dlandry97/Shear_Haptics/Unity_Project/The Haptic Dojo/Assets/SteamVR/Models/Materials/vr_glove_normal.png

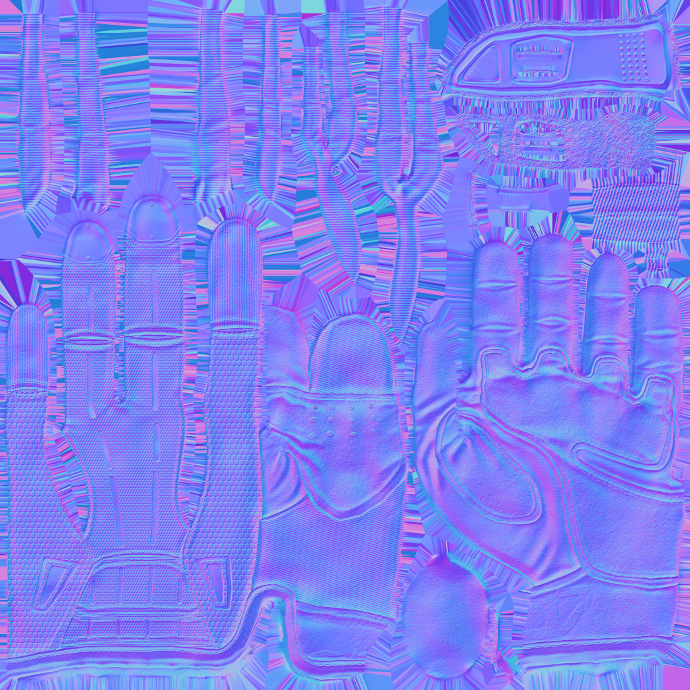
Unity_Project/The Haptic Dojo/Assets/SteamVR/Models/Materials/vr_glove_normal.png
