dlandry97/Shear_Haptics/Unity_Project/The Haptic Dojo/Assets/Katana/Texture/PNG/Katana_AO.png

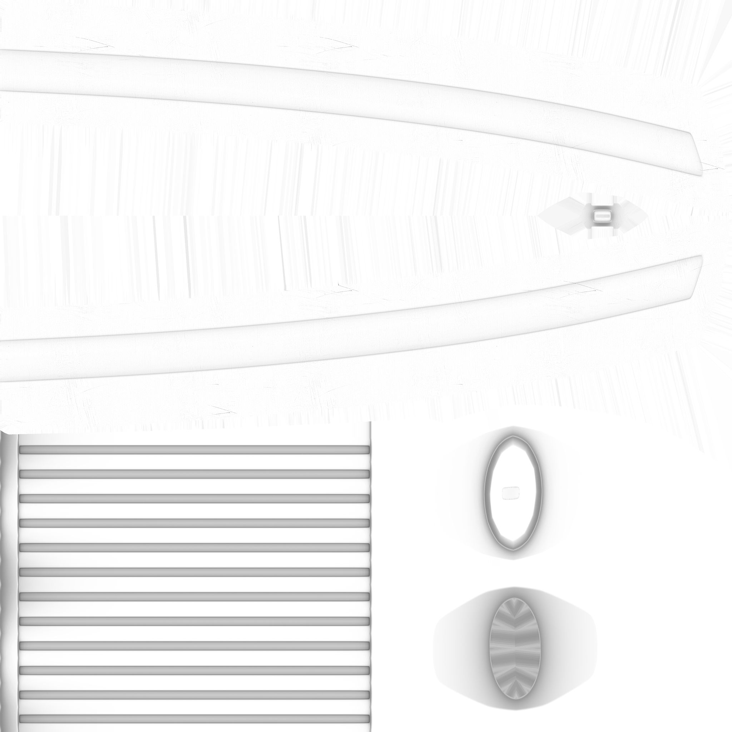
Unity_Project/The Haptic Dojo/Assets/Katana/Texture/PNG/Katana_AO.png
