dlandry97/Shear_Haptics/Unity_Project/The Haptic Dojo/Assets/Katana/Texture/PNG/Katana_Metallic.png

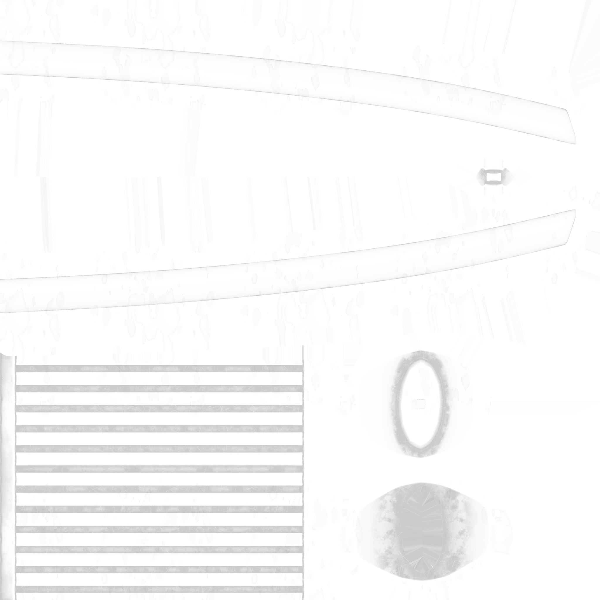
Unity_Project/The Haptic Dojo/Assets/Katana/Texture/PNG/Katana_Metallic.png
