dlandry97/Shear_Haptics/Unity_Project/The Haptic Dojo/Assets/Katana/Texture/PNG/Katana_Normal_DirectX.png

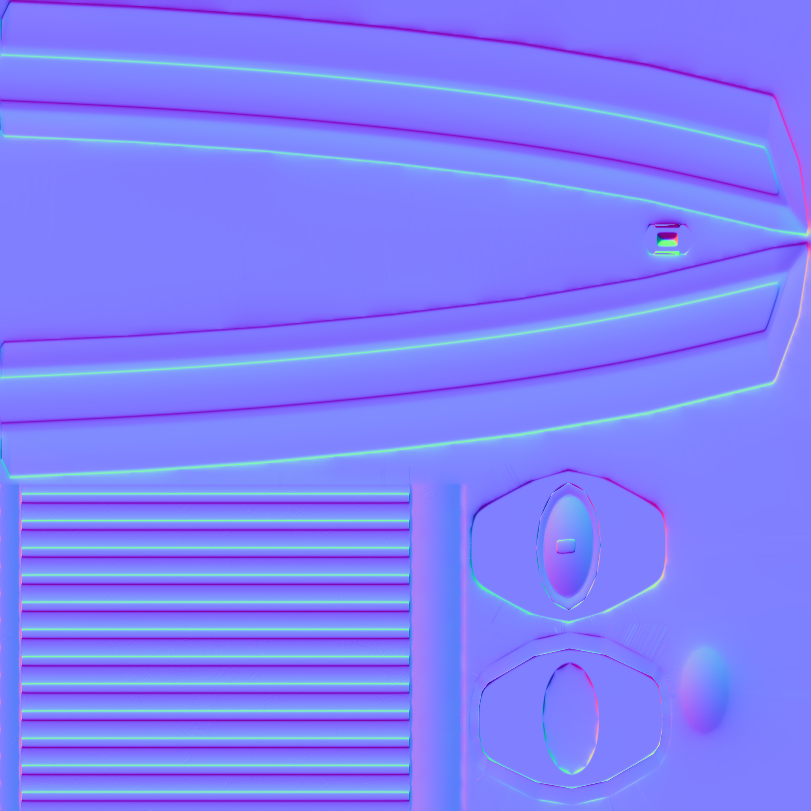
Unity_Project/The Haptic Dojo/Assets/Katana/Texture/PNG/Katana_Normal_DirectX.png
