dlandry97/Shear_Haptics/Unity_Project/The Haptic Dojo/Assets/SteamVR/InteractionSystem/Longbow/Textures/ArrowGlint.png

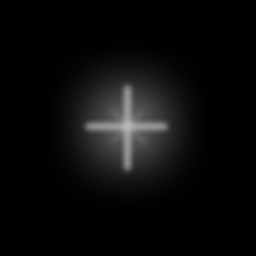
Unity_Project/The Haptic Dojo/Assets/SteamVR/InteractionSystem/Longbow/Textures/ArrowGlint.png
