dlandry97/Shear_Haptics/Unity_Project/The Haptic Dojo/Assets/SteamVR/InteractionSystem/Samples/Grenade/Nade_Nade_Normal.png

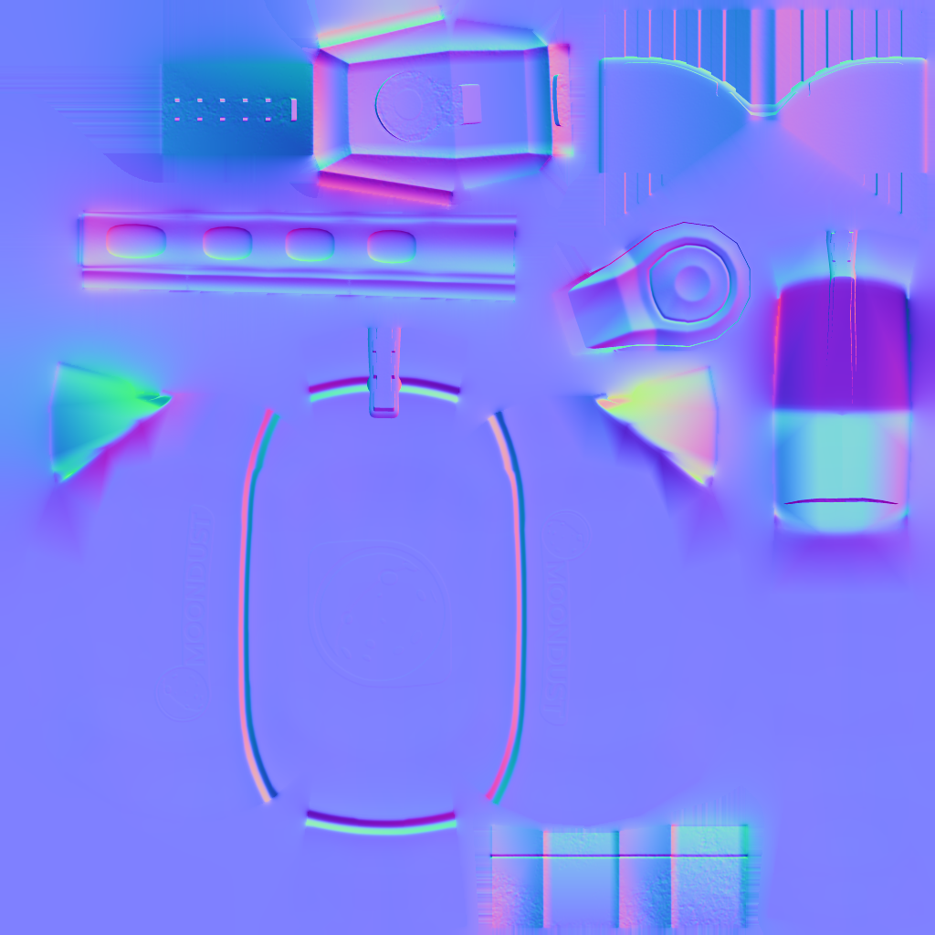
Unity_Project/The Haptic Dojo/Assets/SteamVR/InteractionSystem/Samples/Grenade/Nade_Nade_Normal.png
