dlandry97/Shear_Haptics/Unity_Project/The Haptic Dojo/Assets/SteamVR/InteractionSystem/Samples/Grenade/SunFlare.png

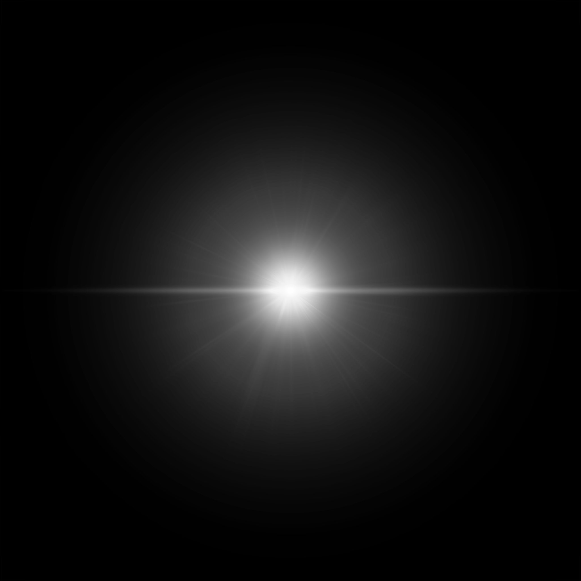
Unity_Project/The Haptic Dojo/Assets/SteamVR/InteractionSystem/Samples/Grenade/SunFlare.png
