dlandry97/Shear_Haptics/Unity_Project/The Haptic Dojo/Assets/SteamVR/InteractionSystem/Samples/JoeJeff/Textures/JJHat_JJHat_AlbedoTransparency.png

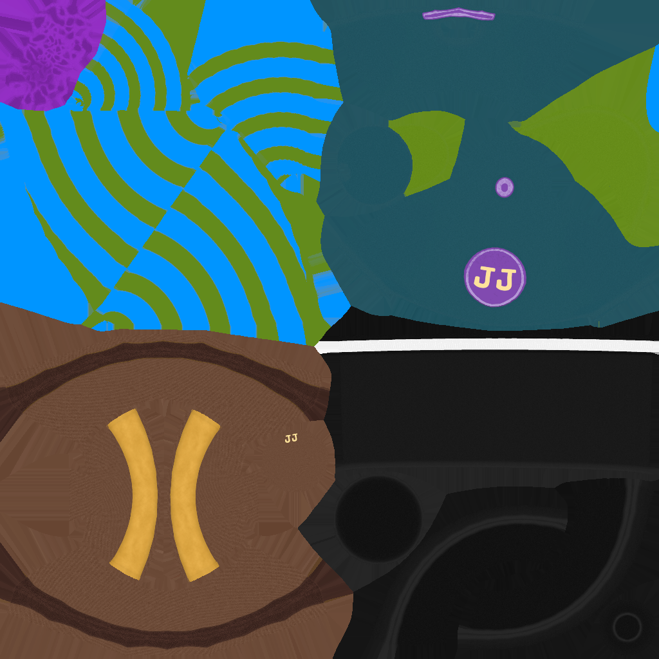
Unity_Project/The Haptic Dojo/Assets/SteamVR/InteractionSystem/Samples/JoeJeff/Textures/JJHat_JJHat_AlbedoTransparency.png
