dlandry97/Shear_Haptics/Unity_Project/The Haptic Dojo/Assets/SteamVR/InteractionSystem/Samples/Models/black_floor_metal_001a.jpg

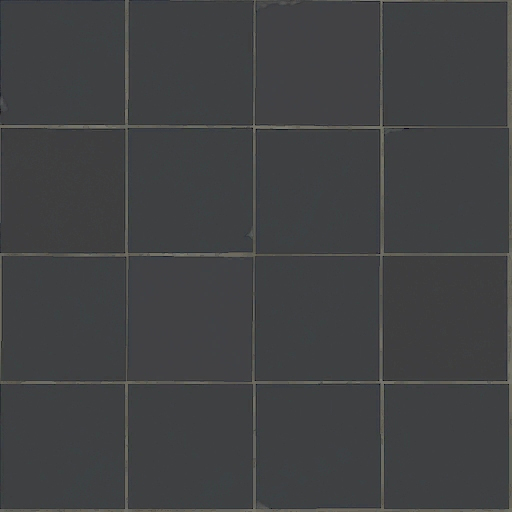
Unity_Project/The Haptic Dojo/Assets/SteamVR/InteractionSystem/Samples/Models/black_floor_metal_001a.jpg
