dlandry97/Shear_Haptics/Unity_Project/The Haptic Dojo/Assets/SteamVR/InteractionSystem/Samples/Squishy/Textures/gooNrm.png

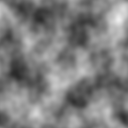
Unity_Project/The Haptic Dojo/Assets/SteamVR/InteractionSystem/Samples/Squishy/Textures/gooNrm.png
