dlandry97/Shear_Haptics/Unity_Project/The Haptic Dojo/Assets/SteamVR/InteractionSystem/Samples/Textures/estimatedOnObject.png

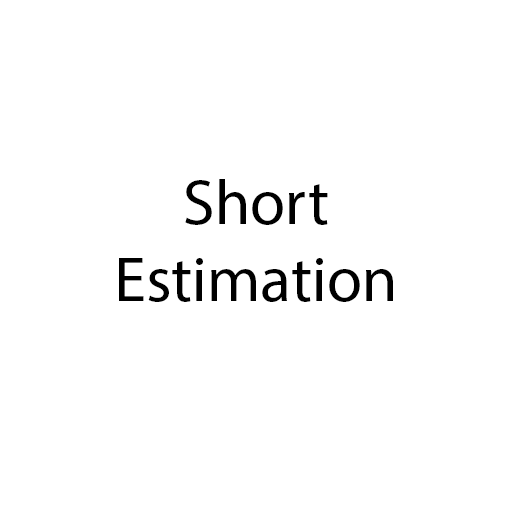
Unity_Project/The Haptic Dojo/Assets/SteamVR/InteractionSystem/Samples/Textures/estimatedOnObject.png
