dlandry97/Shear_Haptics/Unity_Project/The Haptic Dojo/Assets/SteamVR/InteractionSystem/Samples/Textures/fabric nrm.png

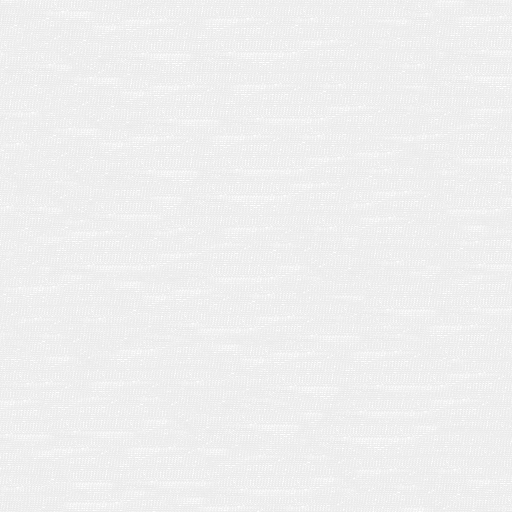
Unity_Project/The Haptic Dojo/Assets/SteamVR/InteractionSystem/Samples/Textures/fabric nrm.png
