dlandry97/Shear_Haptics/Unity_Project/The Haptic Dojo/Assets/SteamVR/Textures/background.png

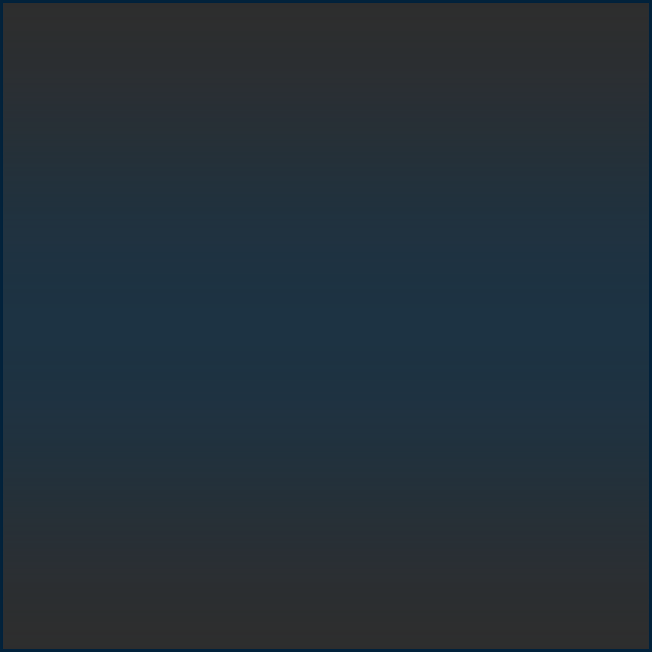
Unity_Project/The Haptic Dojo/Assets/SteamVR/Textures/background.png
