dlandry97/Shear_Haptics/Unity_Project/The Haptic Dojo/Assets/SteamVR/Textures/workshop.png

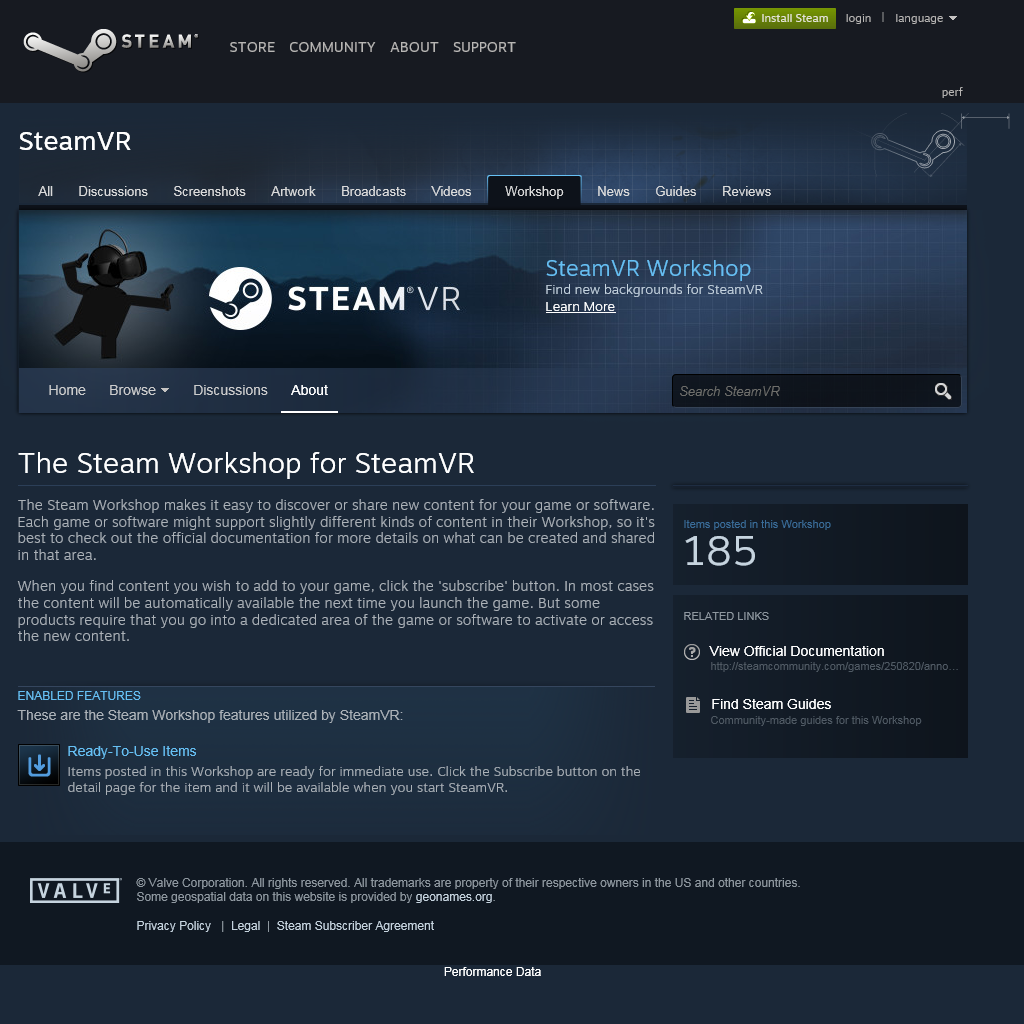
Unity_Project/The Haptic Dojo/Assets/SteamVR/Textures/workshop.png
