dlandry97/Shear_Haptics/Unity_Project/The Haptic Dojo/Assets/VR Beginner/Scenes/Final/EscapeRoom/Lightmap-1_comp_dir.png

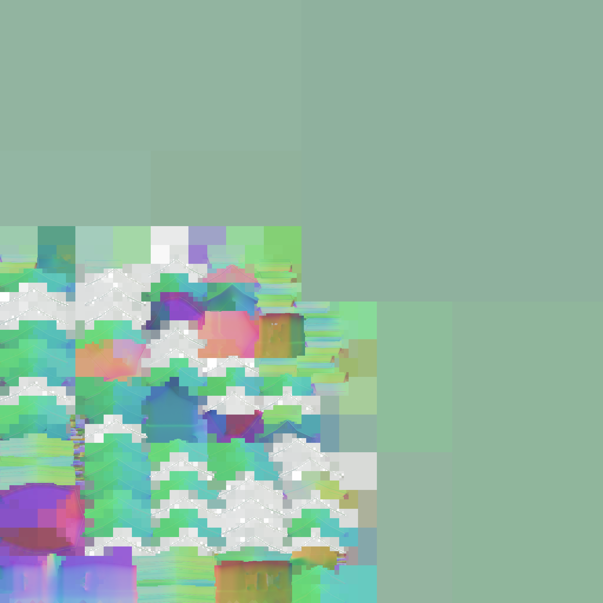
Unity_Project/The Haptic Dojo/Assets/VR Beginner/Scenes/Final/EscapeRoom/Lightmap-1_comp_dir.png
