dlandry97/Shear_Haptics/Unity_Project/The Haptic Dojo/Assets/VR Beginner/Scenes/Final/PrototypeScene/Lightmap-0_comp_dir.png

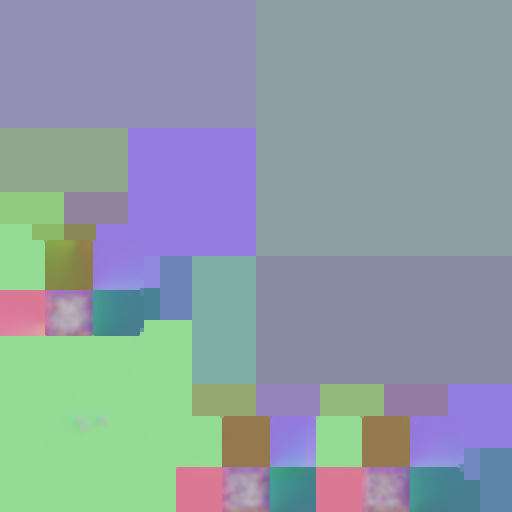
Unity_Project/The Haptic Dojo/Assets/VR Beginner/Scenes/Final/PrototypeScene/Lightmap-0_comp_dir.png
