dlandry97/Shear_Haptics/Unity_Project/The Haptic Dojo/Assets/VR Beginner/Textures/DimmerSwitch/DimmerSwitchBase.png

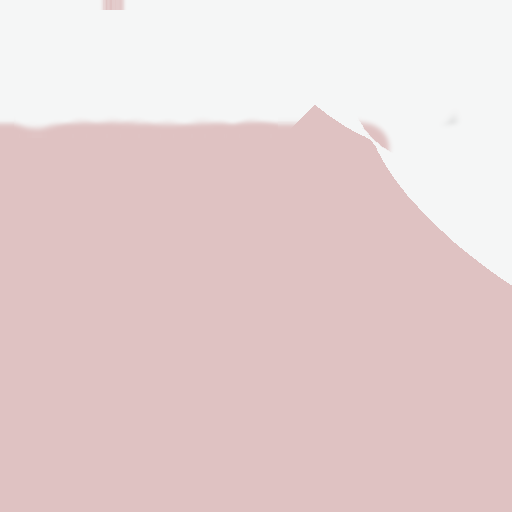
Unity_Project/The Haptic Dojo/Assets/VR Beginner/Textures/DimmerSwitch/DimmerSwitchBase.png
