dlandry97/Shear_Haptics/Unity_Project/The Haptic Dojo/Assets/VR Beginner/Textures/Flashlight/FlashlightBase.png

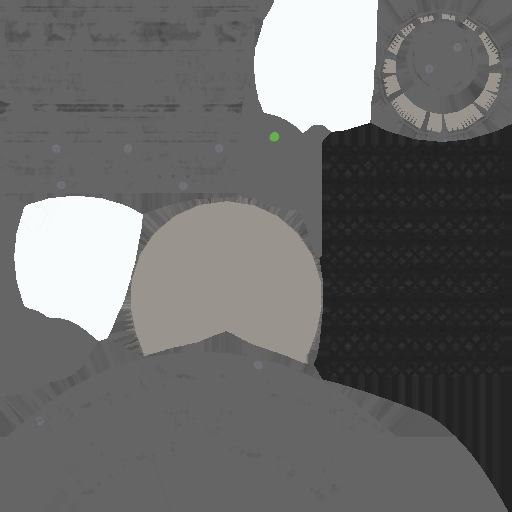
Unity_Project/The Haptic Dojo/Assets/VR Beginner/Textures/Flashlight/FlashlightBase.png
