dlandry97/Shear_Haptics/Unity_Project/The Haptic Dojo/Assets/VR Beginner/Textures/Flashlight/FlashlightNormal.png

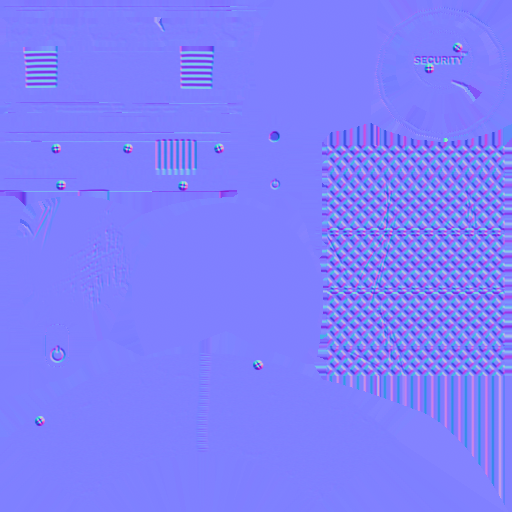
Unity_Project/The Haptic Dojo/Assets/VR Beginner/Textures/Flashlight/FlashlightNormal.png
