dlandry97/Shear_Haptics/Unity_Project/The Haptic Dojo/Assets/VR Beginner/Textures/Fuse/FuseboxOcclusion.png

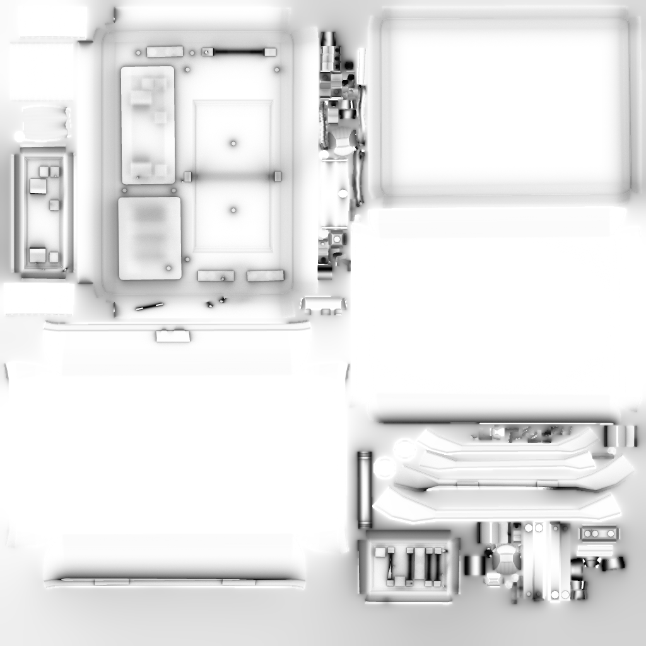
Unity_Project/The Haptic Dojo/Assets/VR Beginner/Textures/Fuse/FuseboxOcclusion.png
