dlandry97/Shear_Haptics/Unity_Project/The Haptic Dojo/Assets/VR Beginner/Textures/Hourglass/SandBase.png

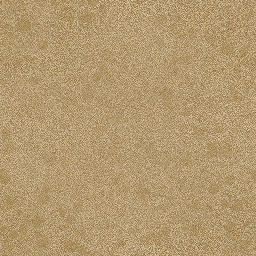
Unity_Project/The Haptic Dojo/Assets/VR Beginner/Textures/Hourglass/SandBase.png
