dlandry97/Shear_Haptics/Unity_Project/The Haptic Dojo/Assets/VR Beginner/Textures/RemoteController/RemoteControllerOcclusion.png

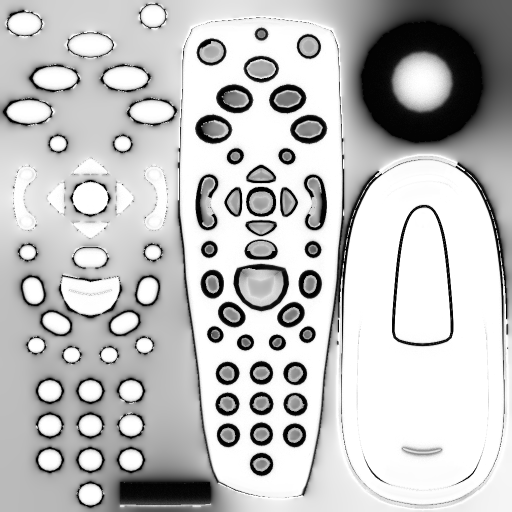
Unity_Project/The Haptic Dojo/Assets/VR Beginner/Textures/RemoteController/RemoteControllerOcclusion.png
