dlandry97/Shear_Haptics/Unity_Project/The Haptic Dojo/Assets/VR Beginner/Textures/Smartwatch/SmartwatchOcclusion.png

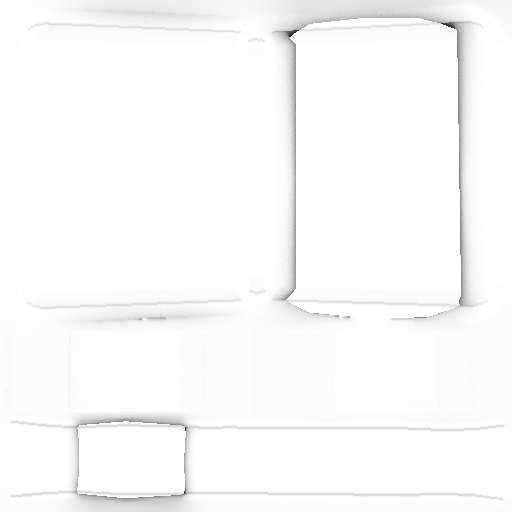
Unity_Project/The Haptic Dojo/Assets/VR Beginner/Textures/Smartwatch/SmartwatchOcclusion.png
