dlandry97/Shear_Haptics/Unity_Project/The Haptic Dojo/Assets/VR Beginner/Textures/Toothbrush/ToothbrushBase.png

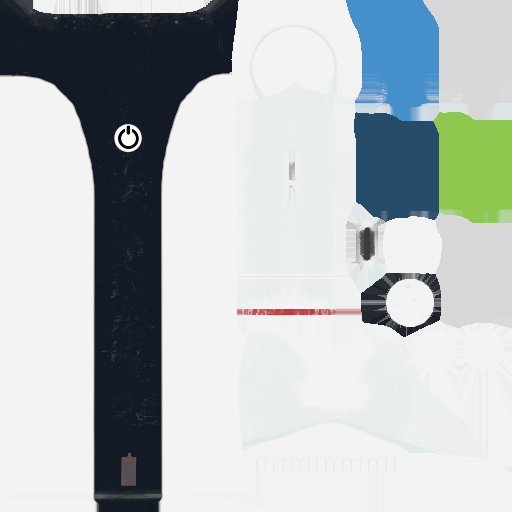
Unity_Project/The Haptic Dojo/Assets/VR Beginner/Textures/Toothbrush/ToothbrushBase.png
