dlandry97/Shear_Haptics/Unity_Project/The Haptic Dojo/Assets/VR Beginner/Textures/Toothbrush/ToothbrushNormal.png

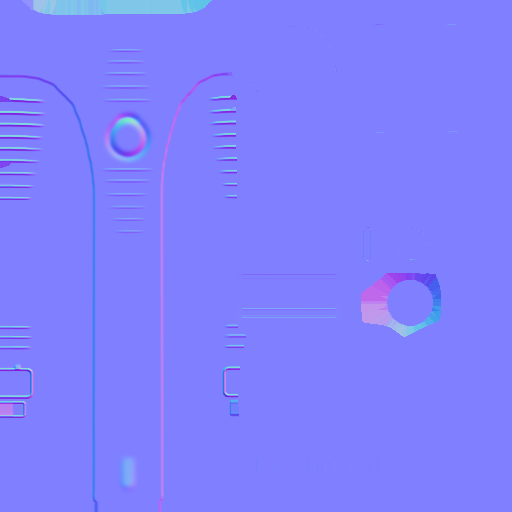
Unity_Project/The Haptic Dojo/Assets/VR Beginner/Textures/Toothbrush/ToothbrushNormal.png
