dlandry97/Shear_Haptics/Unity_Project/The Haptic Dojo/Assets/VR Beginner/VFX/Potions/liquid_sprite.png

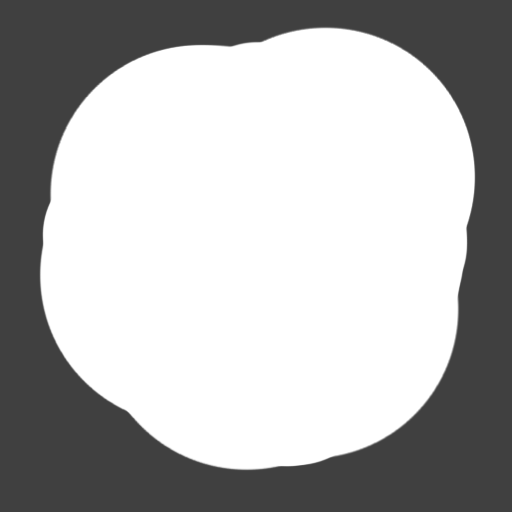
Unity_Project/The Haptic Dojo/Assets/VR Beginner/VFX/Potions/liquid_sprite.png
