dlandry97/Shear_Haptics/Unity_Project/The Haptic Dojo/Assets/VR Beginner/VFX/Prototype/Artboard 2 copy 2.png

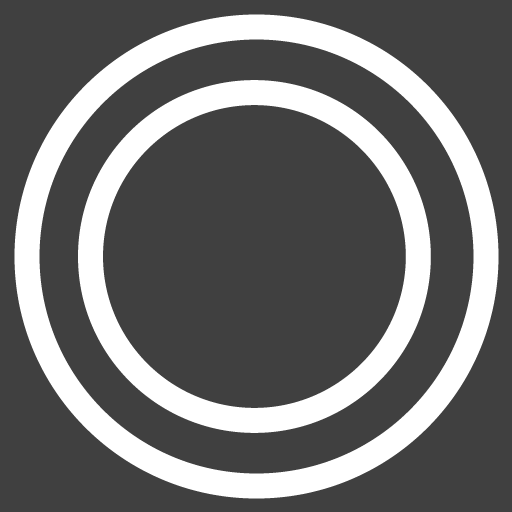
Unity_Project/The Haptic Dojo/Assets/VR Beginner/VFX/Prototype/Artboard 2 copy 2.png
