dlandry97/Shear_Haptics/Unity_Project/The Haptic Dojo/Assets/VR Beginner/VFX/SharedTextures/WitchGlyphs.png

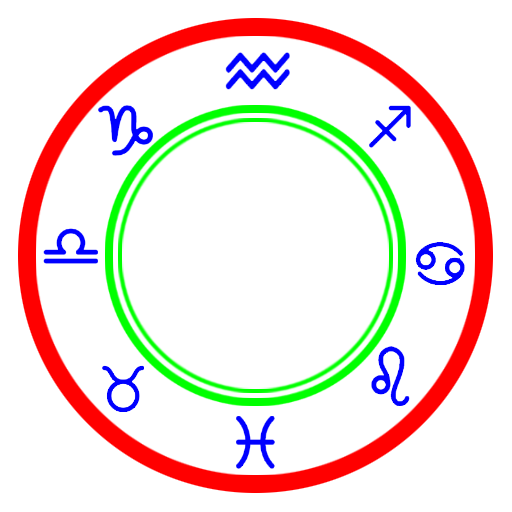
Unity_Project/The Haptic Dojo/Assets/VR Beginner/VFX/SharedTextures/WitchGlyphs.png
