dlandry97/Shear_Haptics/Unity_Project/The Haptic Dojo/Assets/SteamVR/Models/Materials/AlienHand_MetallicSmoothness.png

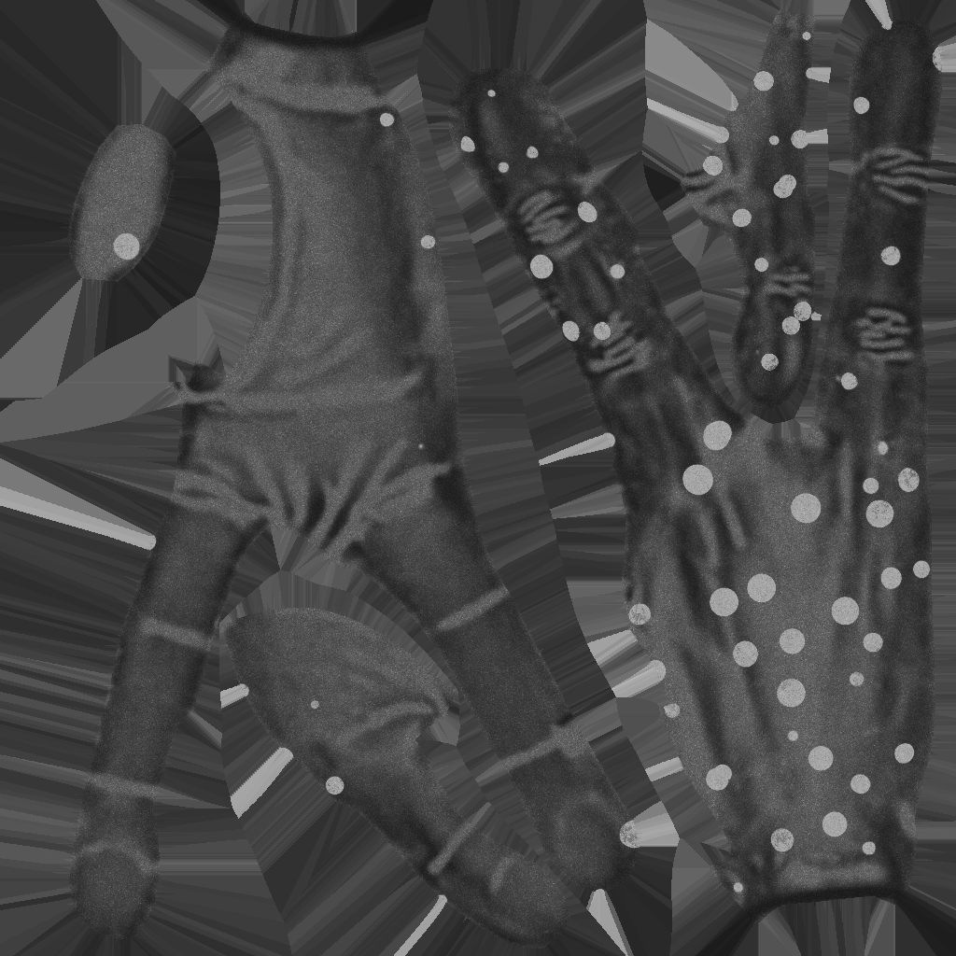
Unity_Project/The Haptic Dojo/Assets/SteamVR/Models/Materials/AlienHand_MetallicSmoothness.png
