dlandry97/Shear_Haptics/Unity_Project/The Haptic Dojo/Assets/SteamVR/Models/Materials/AlienHand_Normal.png

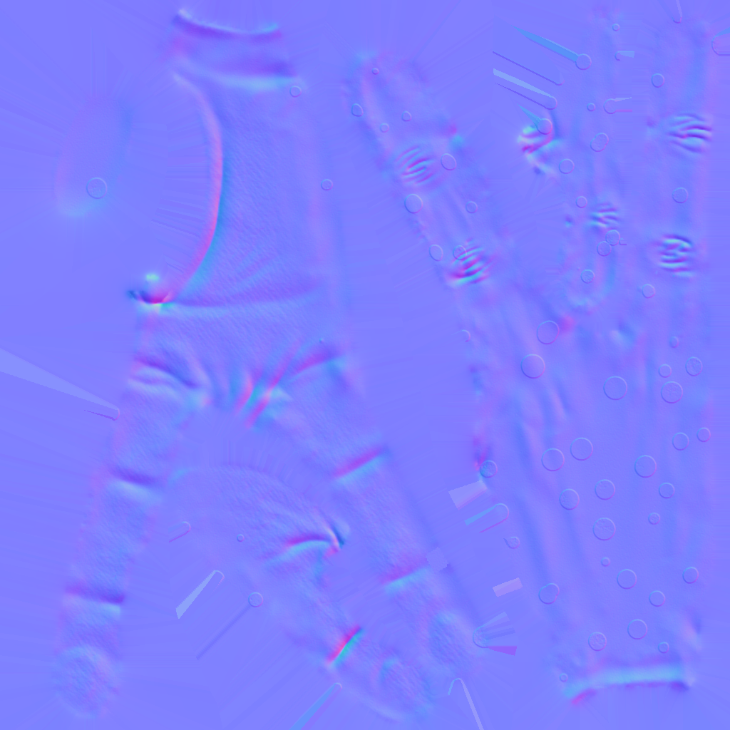
Unity_Project/The Haptic Dojo/Assets/SteamVR/Models/Materials/AlienHand_Normal.png
