dlandry97/Shear_Haptics/Unity_Project/The Haptic Dojo/Assets/SteamVR/Models/Materials/floppyHand Emit.png

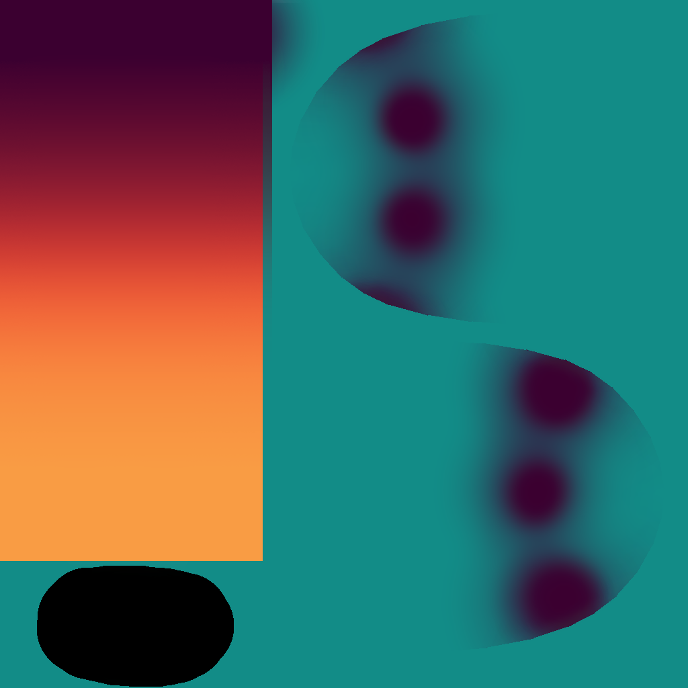
Unity_Project/The Haptic Dojo/Assets/SteamVR/Models/Materials/floppyHand Emit.png
