dlandry97/Shear_Haptics/Unity_Project/The Haptic Dojo/Assets/SteamVR/Models/Materials/vr_glove_color.jpg

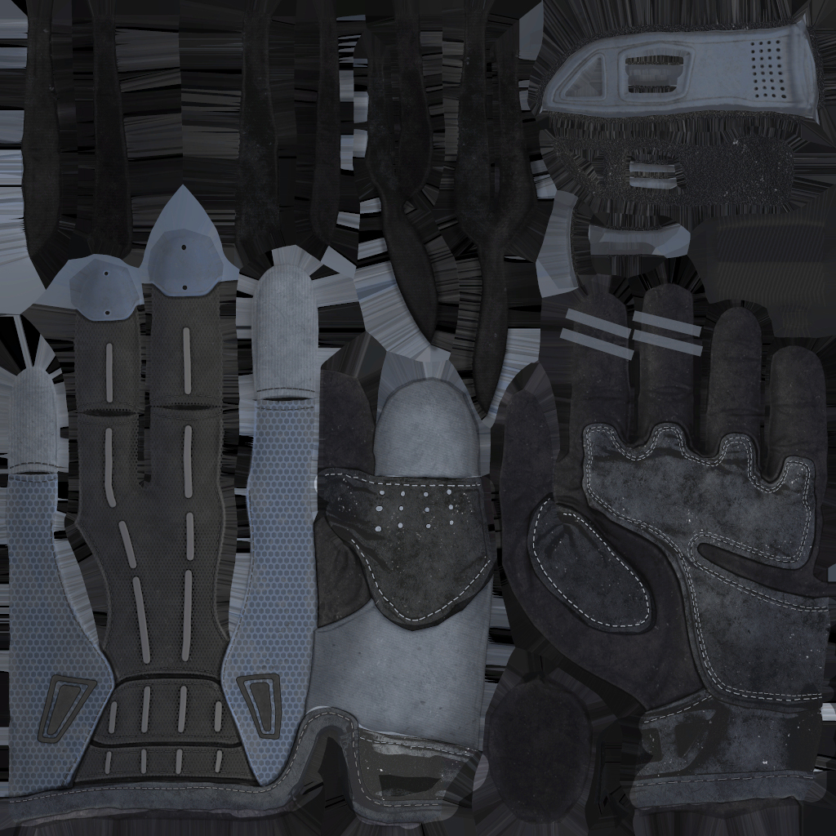
Unity_Project/The Haptic Dojo/Assets/SteamVR/Models/Materials/vr_glove_color.jpg
