dlandry97/Shear_Haptics/Unity_Project/The Haptic Dojo/Assets/VR Beginner/Materials/Skybox.png

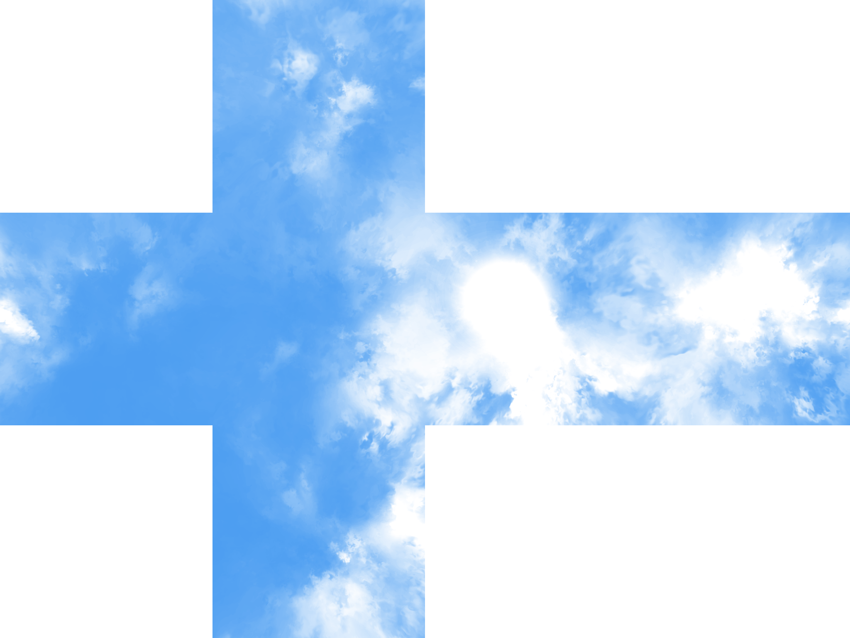
Unity_Project/The Haptic Dojo/Assets/VR Beginner/Materials/Skybox.png
