dlandry97/Shear_Haptics/Unity_Project/The Haptic Dojo/Assets/VR Beginner/Textures/TheMaterial/TheMaterialMetallic.tif

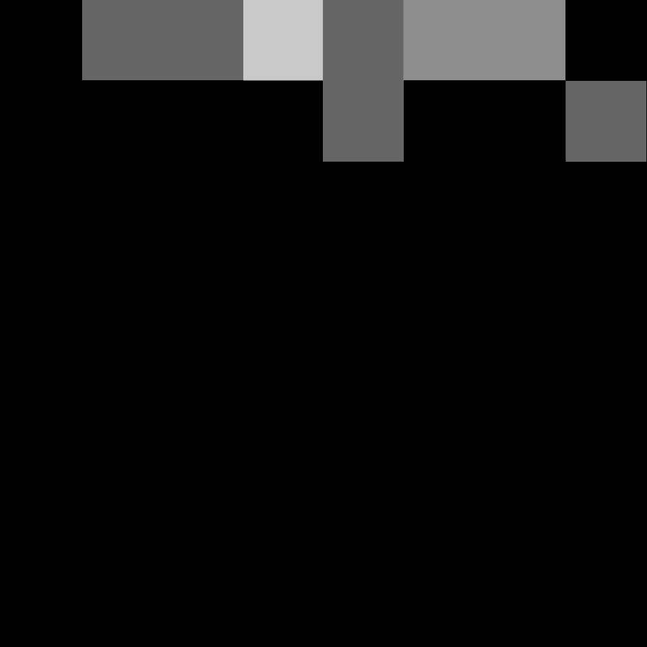
Unity_Project/The Haptic Dojo/Assets/VR Beginner/Textures/TheMaterial/TheMaterialMetallic.tif
